cmichalsen/Haptic_Vest/Haptic_Game_Server/Constants.py

# Minimum time between motor commands
TIME_INTERVAL = 40

# Scale time.sleep functions in milliseconds.
TIME_SCALE = 0.001

# Time between each command during constant time effects
TIME_CONST = 50

# Amount of motor power to fluctuate when fading in/out
FADE_IN_FADE_OUT = 0.2

# Set minimum % power for PWM output (For Capsule Motors)
MOTOR_MINIMUM_POWER = 0.1

# For testing with LEDs
# MOTOR_MINIMUM_POWER = 0.0
